cdntinker/TinkerLink/3D/Cf-Cm.step

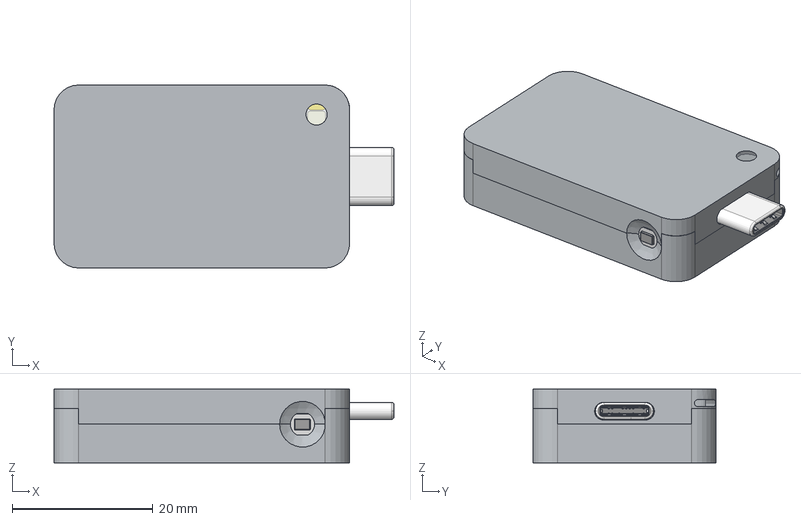
[picture p20: CAD file, 2026-10-09]
3D/Cf-Cm.step
48.3 x 26.0 x 10.5 mm
Da Bottom (Cf-Cm)
Da Top (Cf-Cm)
LightPipe012
TinkerLink_PCB004
LED-SMD_6P-L3.5-W3.5_SK6812MINIRGBW-WS-P6-A005
SW-SMD_K2-1847DT-A4SA-006
USB-C-SMD out004
USB_C_Receptacle in004
