cdntinker/TinkerLink/Hardware/KiCAD_Customs/Antenna-thingy-straight.step

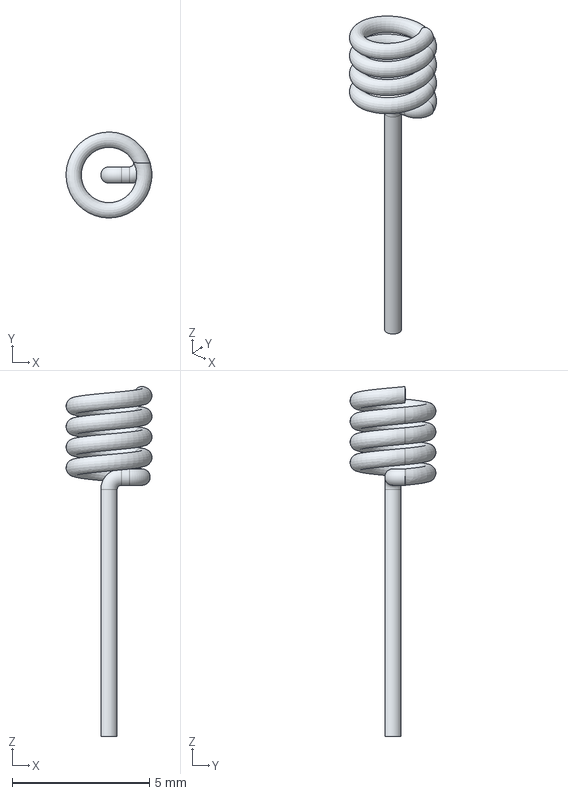
[picture p21: CAD file, 2026-09-28]
Hardware/KiCAD_Customs/Antenna-thingy-straight.step
3.13 x 3.13 x 12.7 mm
