cdntinker/TinkerLink/3D/Am-Cm.step

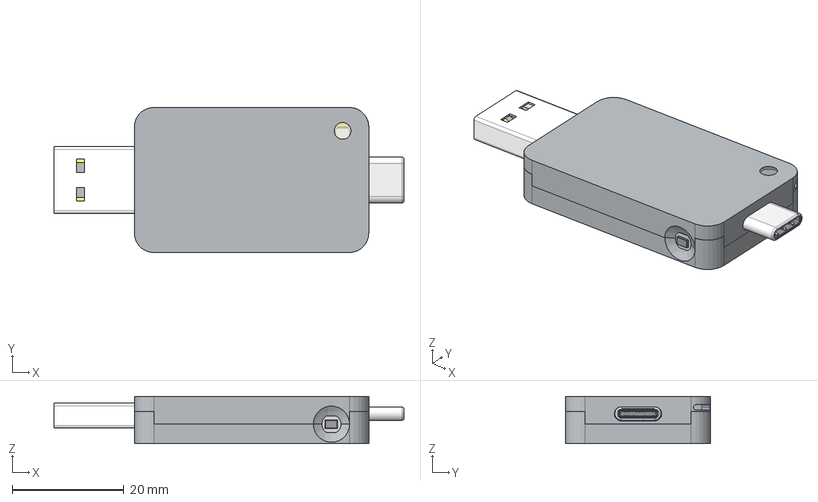
[picture p22: CAD file, 2026-10-09]
3D/Am-Cm.step
62.7 x 26.0 x 8.50 mm
Da Bottom (M-M)
Da Top (M-M)
LightPipe010
LED-SMD_6P-L3.5-W3.5_SK6812MINIRGBW-WS-P6-A003
SW-SMD_K2-1847DT-A4SA-004
USB-A-SMD in002
USB-C-SMD out002
