cdntinker/TinkerLink/3D/Cf-Cf.step

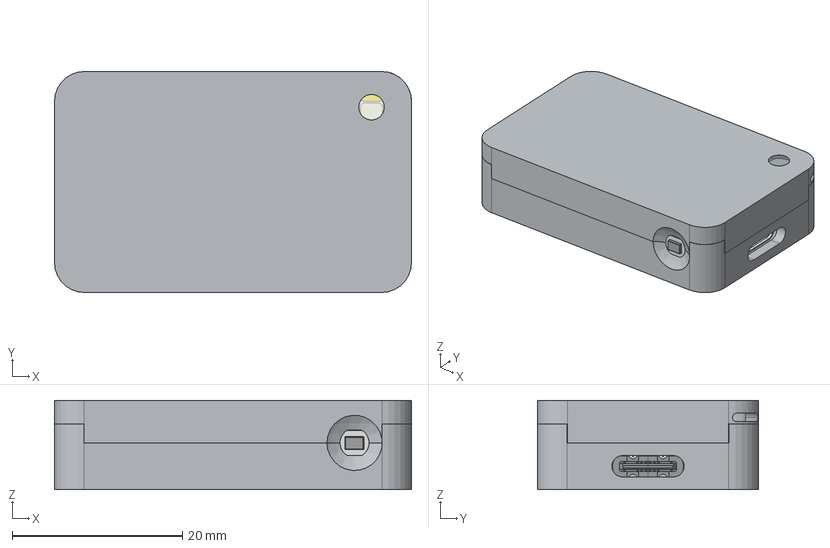
[picture p23: CAD file, 2026-10-09]
3D/Cf-Cf.step
42.0 x 26.0 x 10.5 mm
Da Bottom (Cf-Cf)
Da Top (Cf-Cf)
LightPipe013
TinkerLink_PCB005
LED-SMD_6P-L3.5-W3.5_SK6812MINIRGBW-WS-P6-A006
SW-SMD_K2-1847DT-A4SA-007
USB_C_Receptacle in005
USB_C_Receptacleout005
